MOSH-Insa-Toulouse/2024-2025-4GP-Yoann-LyHai-VietHoang/README_Image/Schema_KiCad.jpg

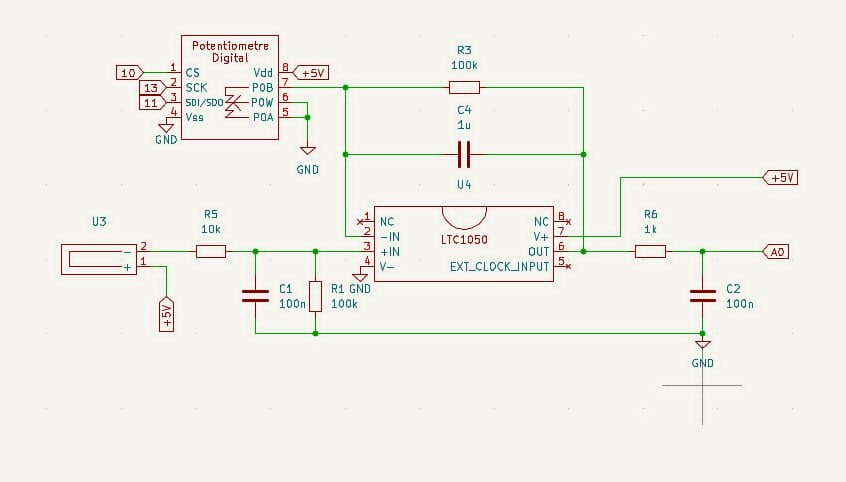
README_Image/Schema_KiCad.jpg
