MOSH-Insa-Toulouse/2024-2025-4GP-Yoann-LyHai-VietHoang/Capteur_KICAD/Librairie_Model3D/bluetooth-module-hc-05-1.snapshot.4/Bluetooth Module HC-05/HC-05 part5.SLDPRT

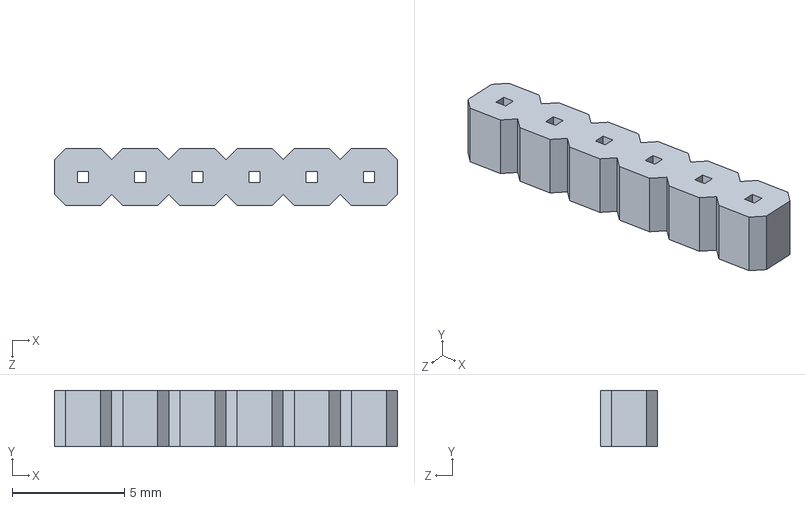
[picture p45: CAD file, 2025-05-29]
Capteur_KICAD/Librairie_Model3D/bluetooth-module-hc-05-1.snapshot.4/Bluetooth Module HC-05/HC-05 part5.SLDPRT
15.3 x 2.50 x 2.55 mm
