MOSH-Insa-Toulouse/2024-2025-4GP-Yoann-LyHai-VietHoang/Capteur_KICAD/Librairie_Model3D/flex-sensor-spectra-symbol-1.snapshot.2/Flex Sensor/GoldProngTerminal.SLDPRT

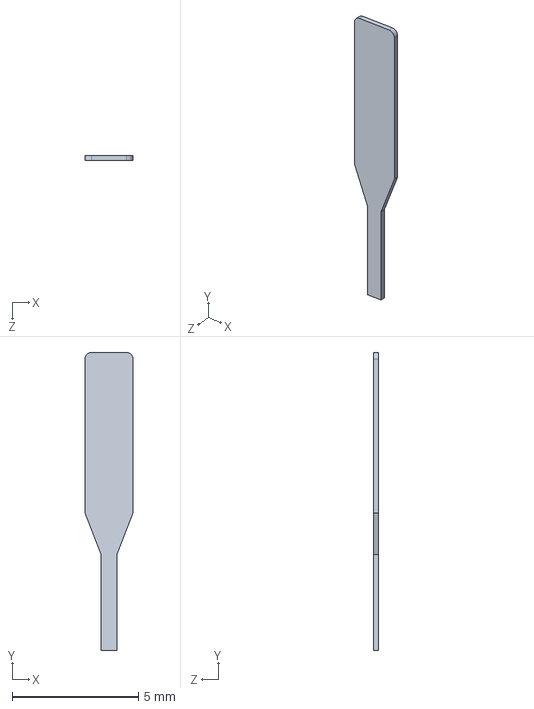
[picture p46: CAD file, 2025-03-12]
Capteur_KICAD/Librairie_Model3D/flex-sensor-spectra-symbol-1.snapshot.2/Flex Sensor/GoldProngTerminal.SLDPRT
1.90 x 11.8 x 0.203 mm
