MOSH-Insa-Toulouse/2024-2025-4GP-Yoann-LyHai-VietHoang/Capteur_KICAD/Librairie_Model3D/bluetooth-module-hc-05-1.snapshot.4/Bluetooth Module HC-05/HC-05 part7.SLDPRT

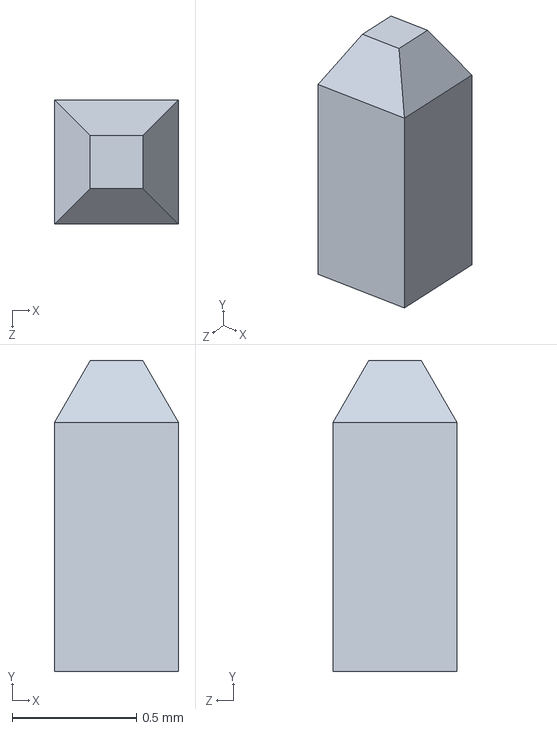
[picture p49: CAD file, 2025-05-29]
Capteur_KICAD/Librairie_Model3D/bluetooth-module-hc-05-1.snapshot.4/Bluetooth Module HC-05/HC-05 part7.SLDPRT
0.5 x 1.25 x 0.5 mm
