MOSH-Insa-Toulouse/2024-2025-4GP-Yoann-LyHai-VietHoang/Capteur_KICAD/Librairie_Model3D/bluetooth-module-hc-05-1.snapshot.4/Bluetooth Module HC-05/tactileswitch-short.SLDPRT

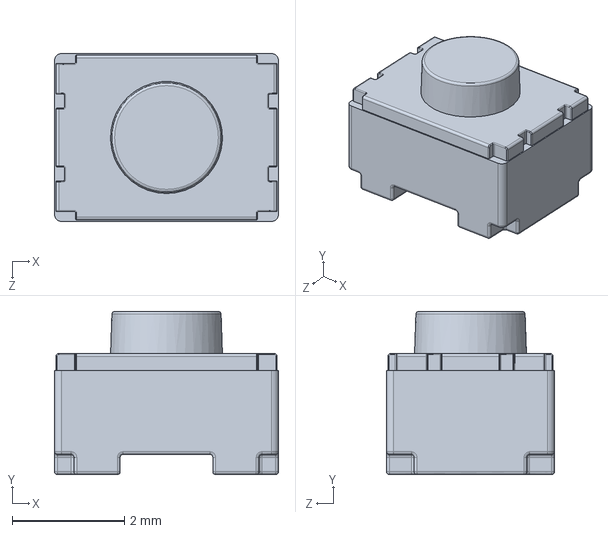
[picture p51: CAD file, 2025-05-29]
Capteur_KICAD/Librairie_Model3D/bluetooth-module-hc-05-1.snapshot.4/Bluetooth Module HC-05/tactileswitch-short.SLDPRT
4.00 x 2.91 x 3.00 mm
