MOSH-Insa-Toulouse/2024-2025-4GP-Yoann-LyHai-VietHoang/Capteur_KICAD/Librairie_Model3D/pin-header-male-2-54mm-different-pin-numbers-1.snapshot.2/18-Pin Header - Male - 2.54mm.step

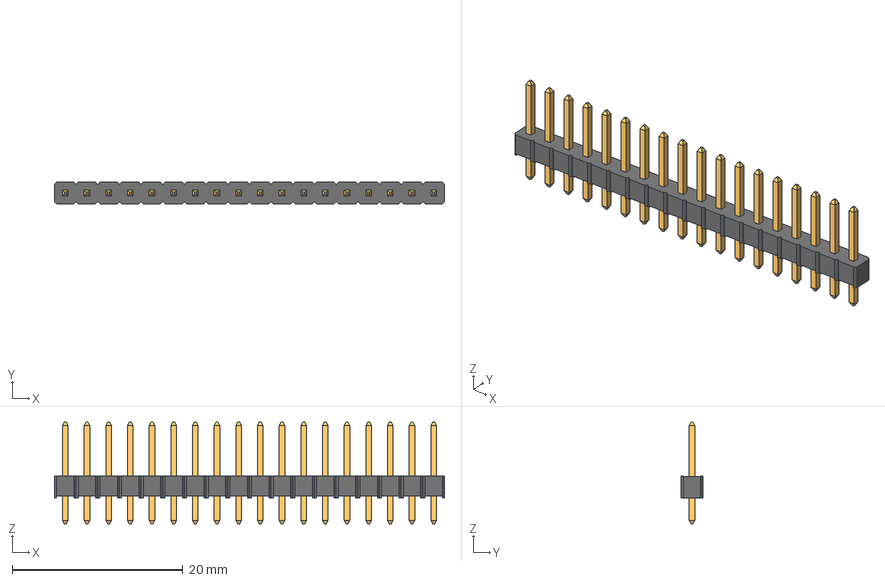
[picture p52: CAD file, 2025-05-29]
Capteur_KICAD/Librairie_Model3D/pin-header-male-2-54mm-different-pin-numbers-1.snapshot.2/18-Pin Header - Male - 2.54mm.step
45.7 x 2.54 x 11.9 mm
