MOSH-Insa-Toulouse/2024-2025-4GP-Yoann-LyHai-VietHoang/Capteur_KICAD/Librairie_Model3D/bluetooth-module-hc-05-1.snapshot.4/Bluetooth Module HC-05/HC-05 part12.SLDPRT

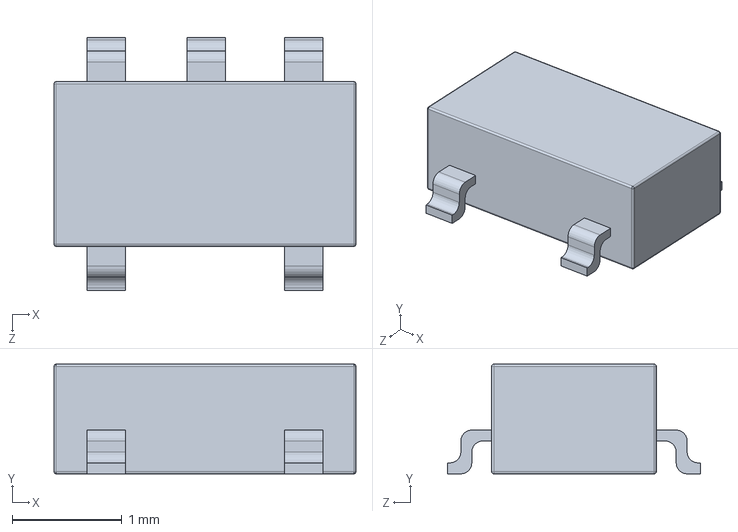
[picture p53: CAD file, 2025-05-29]
Capteur_KICAD/Librairie_Model3D/bluetooth-module-hc-05-1.snapshot.4/Bluetooth Module HC-05/HC-05 part12.SLDPRT
2.75 x 1.00 x 2.30 mm
