MOSH-Insa-Toulouse/2024-2025-4GP-Yoann-LyHai-VietHoang/Capteur_KICAD/Librairie_Model3D/bluetooth-module-hc-05-1.snapshot.4/Bluetooth Module HC-05/HC-05.SLDPRT

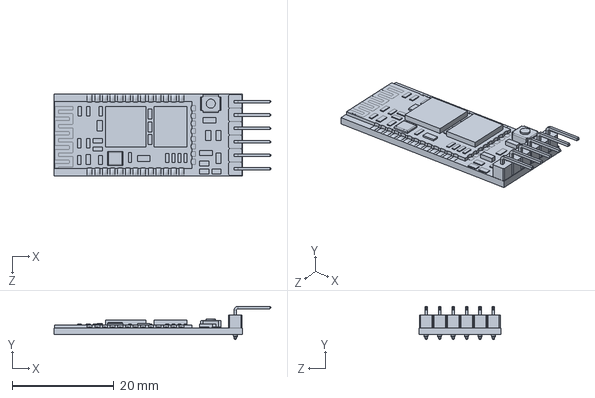
[picture p55: CAD file, 2025-05-29]
Capteur_KICAD/Librairie_Model3D/bluetooth-module-hc-05-1.snapshot.4/Bluetooth Module HC-05/HC-05.SLDPRT
42.6 x 6.55 x 16.0 mm
