MOSH-Insa-Toulouse/2024-2025-4GP-Yoann-LyHai-VietHoang/LTSpice/LTC1050 filtre+amp montage_graphite_sensor.asc

C1: cap; 100n
C2: cap; 100n
C3: cap; 100n
C4: cap; 1µ
R1: res; 100k
R2: res; 1k
R3: res; 100k
R5: res; 10k
R6: res; 1k
Rsensor: res; 10k
U1: LTC1050
V1: voltage; 5
V+: voltage; ""; AC 5 0
Named nets: 0, ADC, Vem, Vep, +5V
;tran 4
.ac dec 200 0.1 0.1G
