MOSH-Insa-Toulouse/2024-2025-4GP-Yoann-LyHai-VietHoang/LTSpice/montage_test_capteur.asc

C1: cap; 100n
C2: cap; 100n
C3: cap; 1p
C4: cap; 1µ
R1: res; 100k
R2: res; 1k
R3: res; 100k
R5: res; 10k
R6: res; 1k
U1: LTC1050
V1: voltage; 5
V2: voltage; SINE(0 325 50)
V3: voltage; PULSE(0 1 0.2 0.1 0.1 20); AC 1 0
X2: capteur_graphique
Named nets: 0, ADC, Vem, Vep, +5V
;.tran 20
.param G0 10n
.param G1 10n
.param R1 100k
.ac oct 100 0.1 10000
