MOSH-Insa-Toulouse/2024-2025-4GP-Yoann-LyHai-VietHoang/LTSpice/capteur_graphique.asc

B1: bi; I=V(Cp,Cn)*(10n+10n*V(Gc,Gn))
C1: cap; 200µ
R1: res; 1k
Named nets: Cn, Cp, Gp, Gc, Gn
