MOSH-Insa-Toulouse/2024-2025-4GP-Yoann-LyHai-VietHoang/LTSpice/filtre passe-bas.asc

C1: cap; 100p
R1: res; 10k
V1: voltage; PULSE(0 1 10u 1u 1u 10u); AC 1 0
Named nets: my_out, 0
;tran 50u
.ac dec 100 1 1G
